armandursei/Proiect-TSC/Images/Display.png

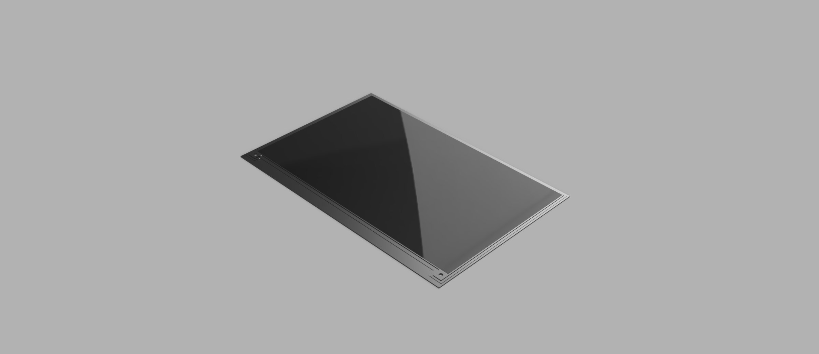
Images/Display.png
