armandursei/Proiect-TSC/Images/EBook_1.PNG

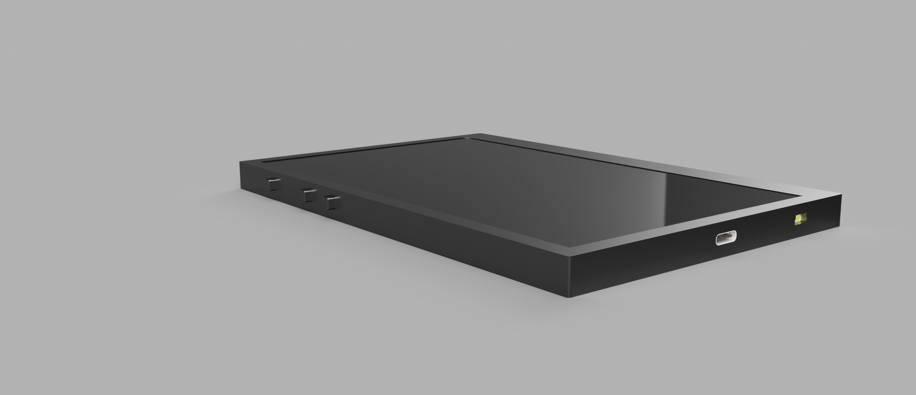
Images/EBook_1.PNG
