armandursei/Proiect-TSC/Images/EBook_inside.png

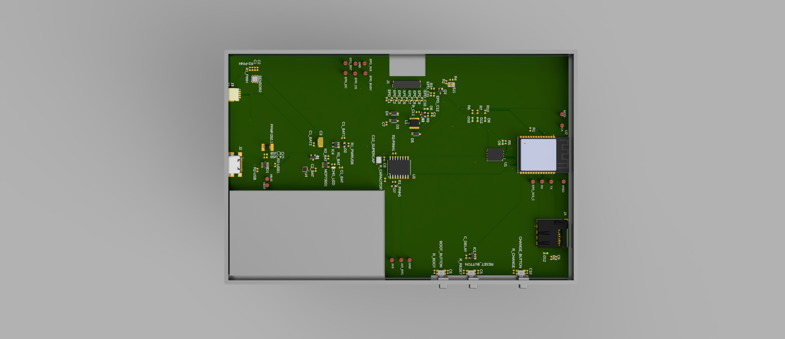
Images/EBook_inside.png
