armandursei/Proiect-TSC/Images/Exploded_1.png

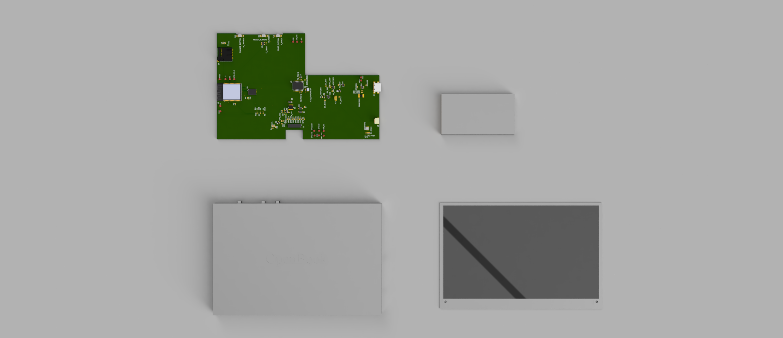
Images/Exploded_1.png
