armandursei/Proiect-TSC/Images/Exploded_2.png

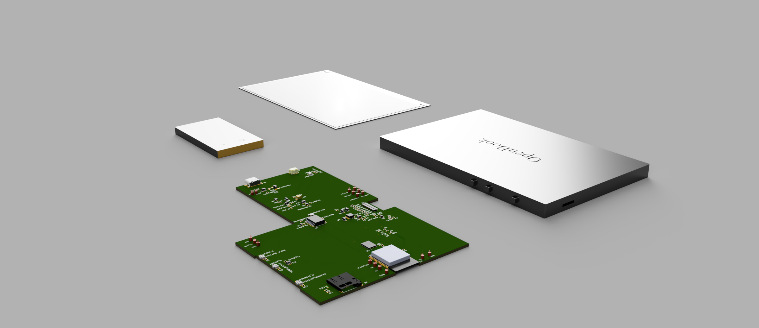
Images/Exploded_2.png
