armandursei/Proiect-TSC/Images/PCB_4.PNG

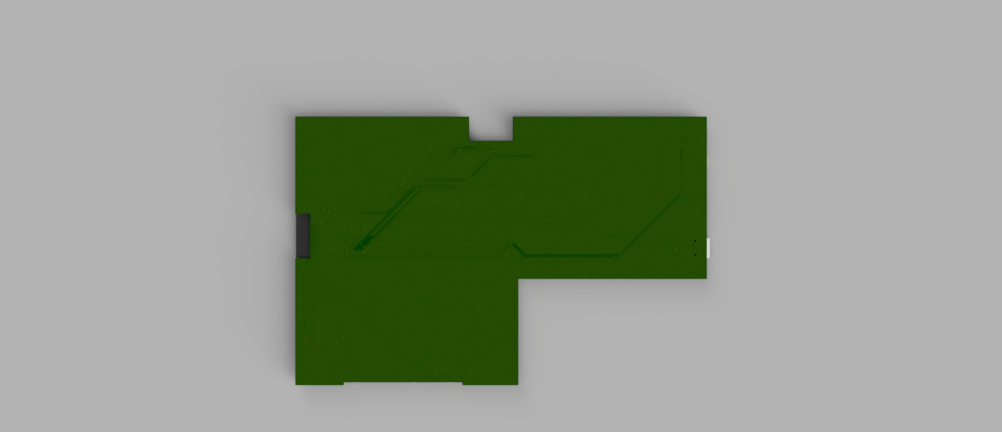
Images/PCB_4.PNG
